romo9840/MFHL_Semesterprojekt_Security/Doku/Schaltplan_Widerstand_neu.png

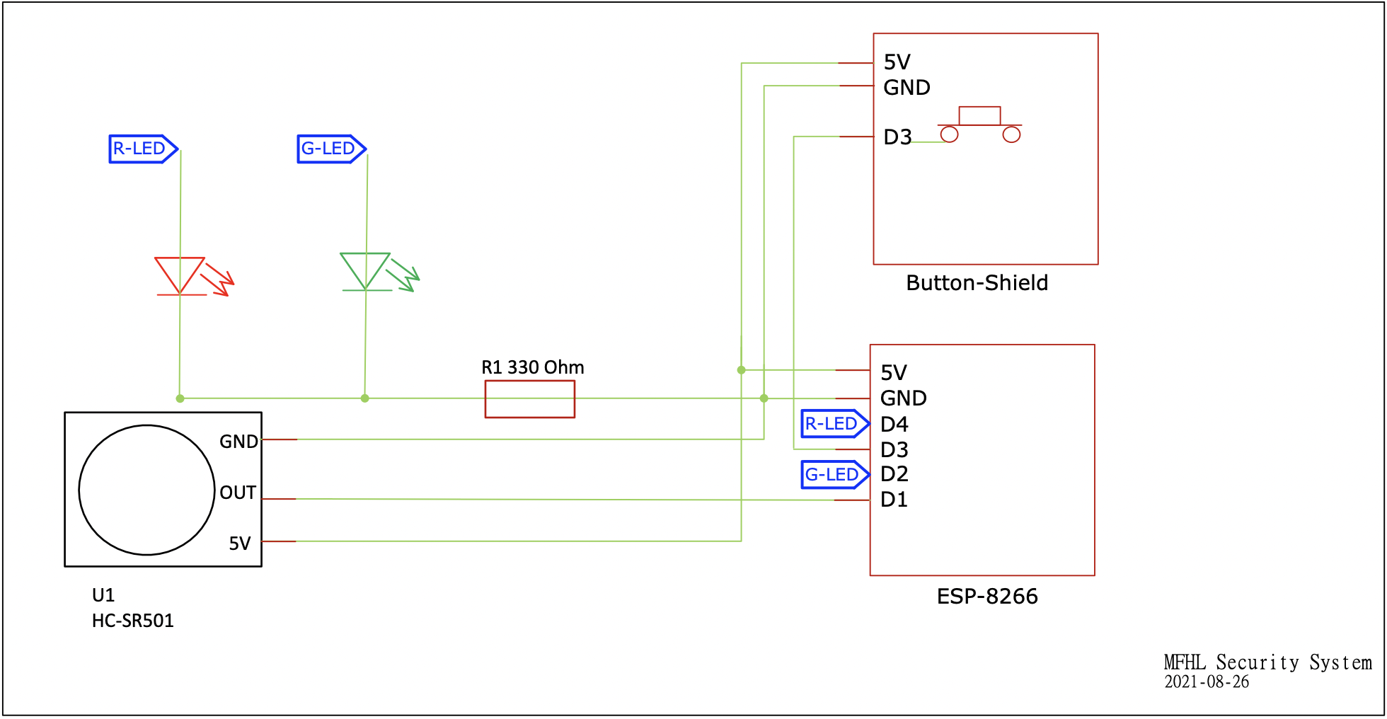
Doku/Schaltplan_Widerstand_neu.png
