romo9840/MFHL_Semesterprojekt_Security/Doku/Zustandsdiagramm_neu.png

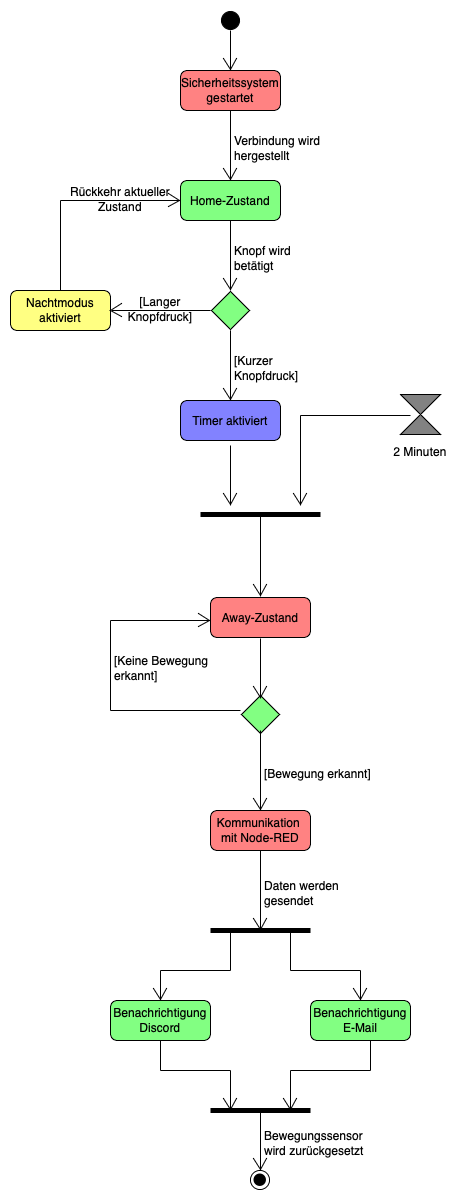
Doku/Zustandsdiagramm_neu.png
