romo9840/MFHL_Semesterprojekt_Security/Pictures/11.09_bare_front.jpg

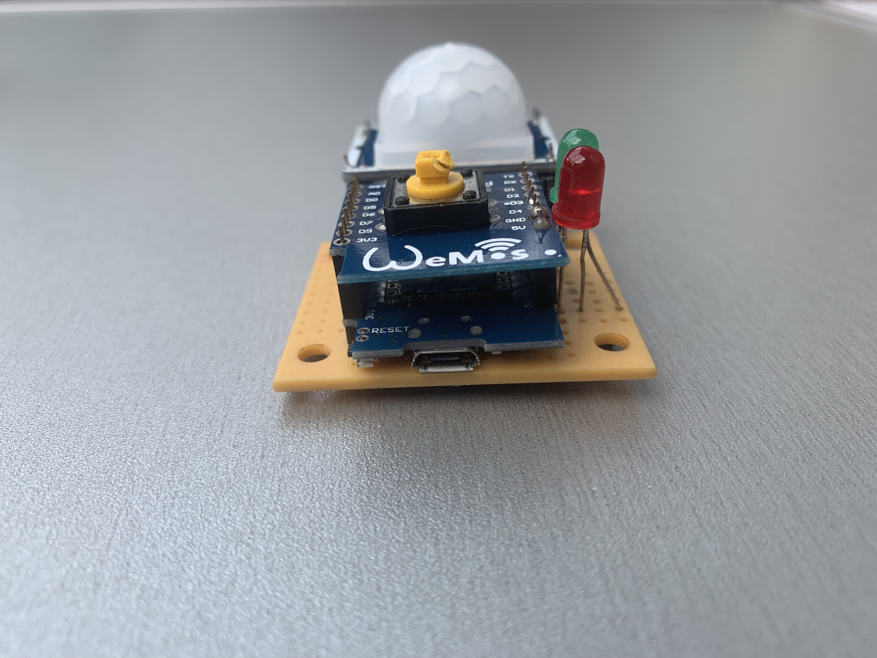
Pictures/11.09_bare_front.jpg
