romo9840/MFHL_Semesterprojekt_Security/Pictures/11.09_bare_other_side3.jpg

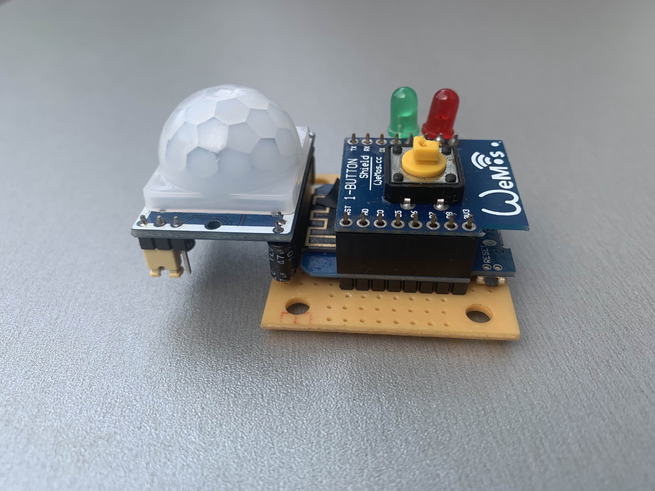
Pictures/11.09_bare_other_side3.jpg
