romo9840/MFHL_Semesterprojekt_Security/Pictures/11.09_bare_top_button.jpg

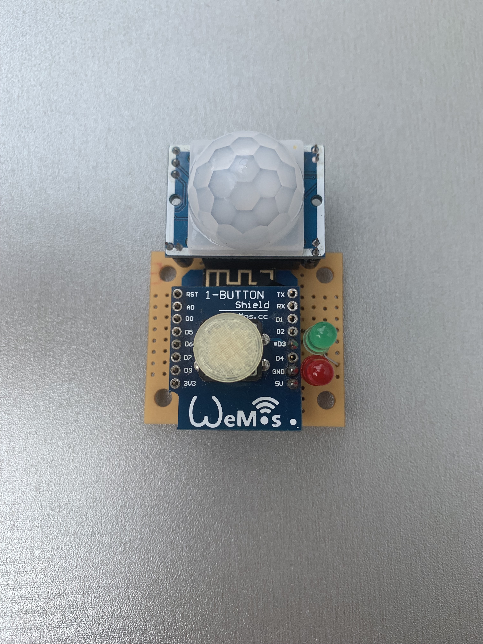
Pictures/11.09_bare_top_button.jpg
