romo9840/MFHL_Semesterprojekt_Security/Pictures/11.09_case_front.jpg

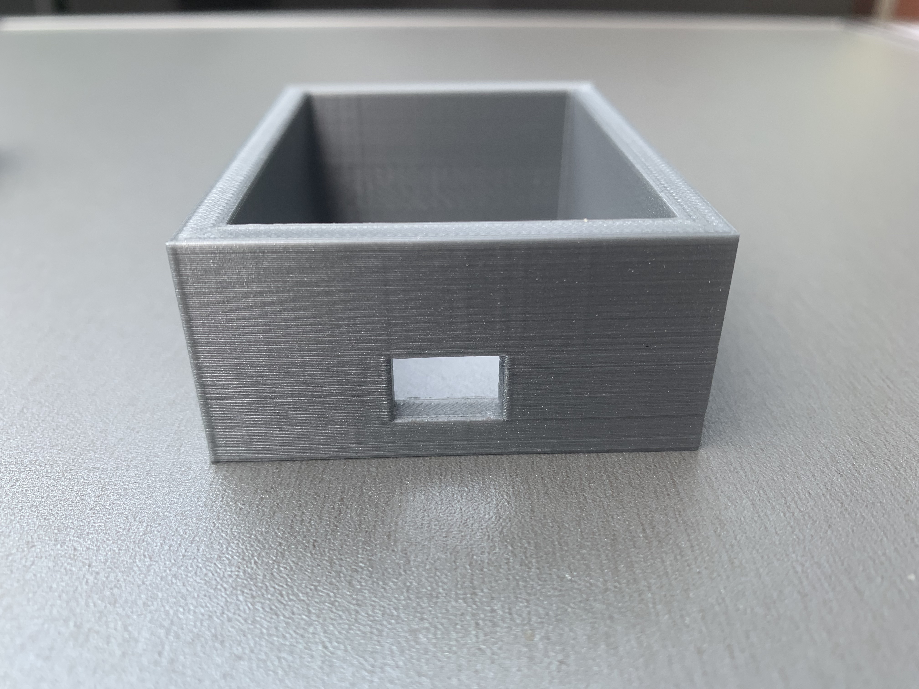
Pictures/11.09_case_front.jpg
