romo9840/MFHL_Semesterprojekt_Security/Pictures/11.09_closer_full_top.jpg

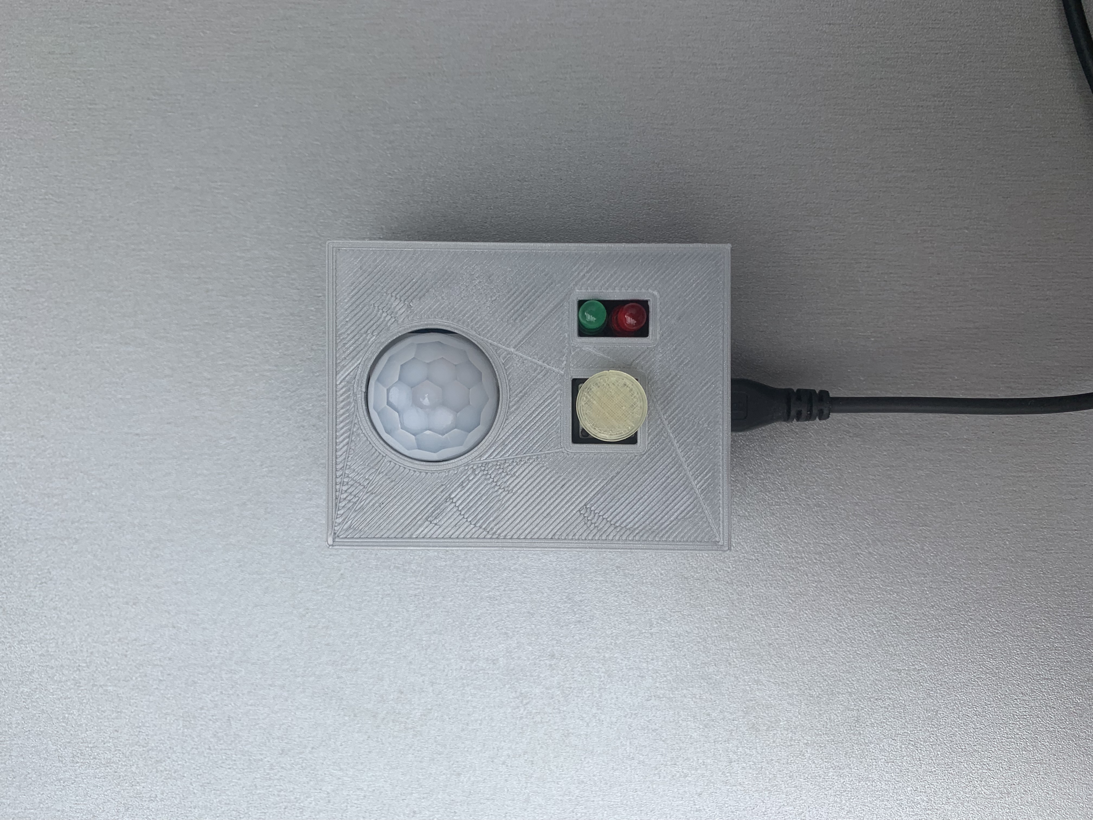
Pictures/11.09_closer_full_top.jpg
