romo9840/MFHL_Semesterprojekt_Security/Pictures/11.09_deckel_side.jpg

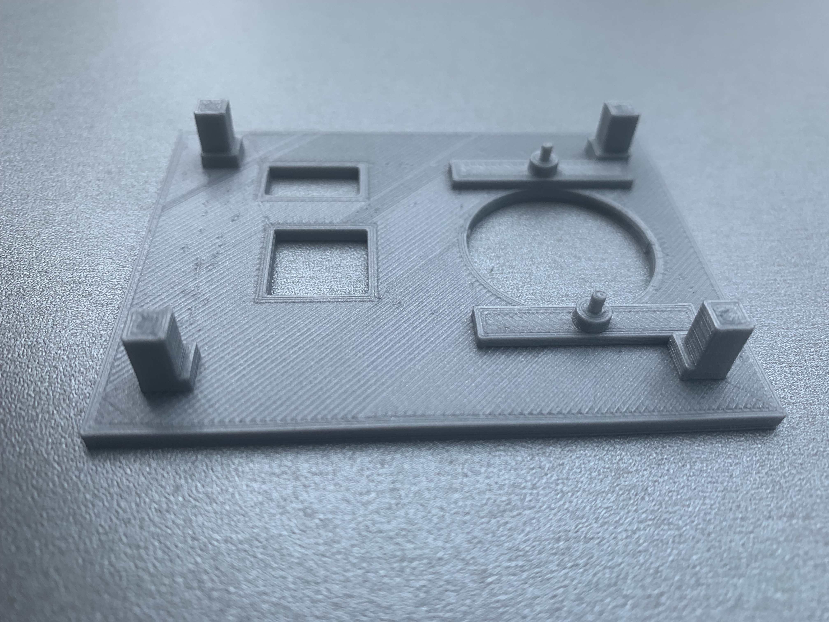
Pictures/11.09_deckel_side.jpg
