romo9840/MFHL_Semesterprojekt_Security/Pictures/11.09_open_top.jpg

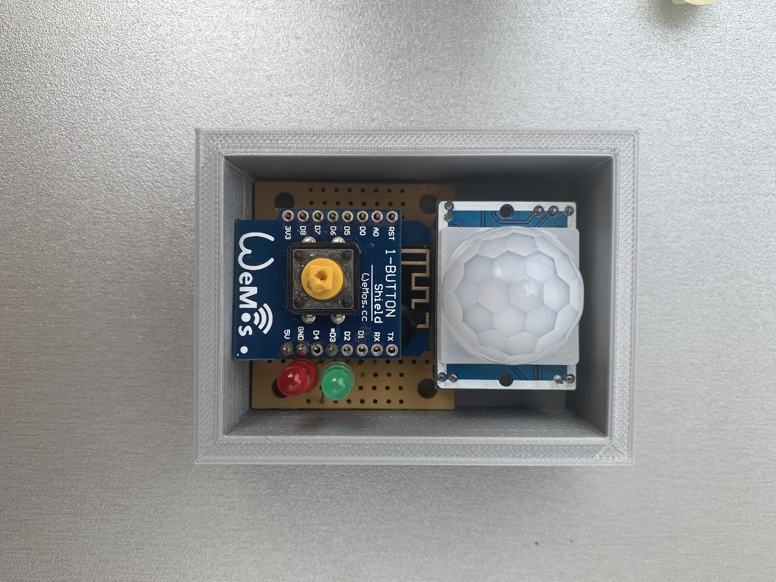
Pictures/11.09_open_top.jpg
