romo9840/MFHL_Semesterprojekt_Security/Pictures/11.09_sensor.jpg

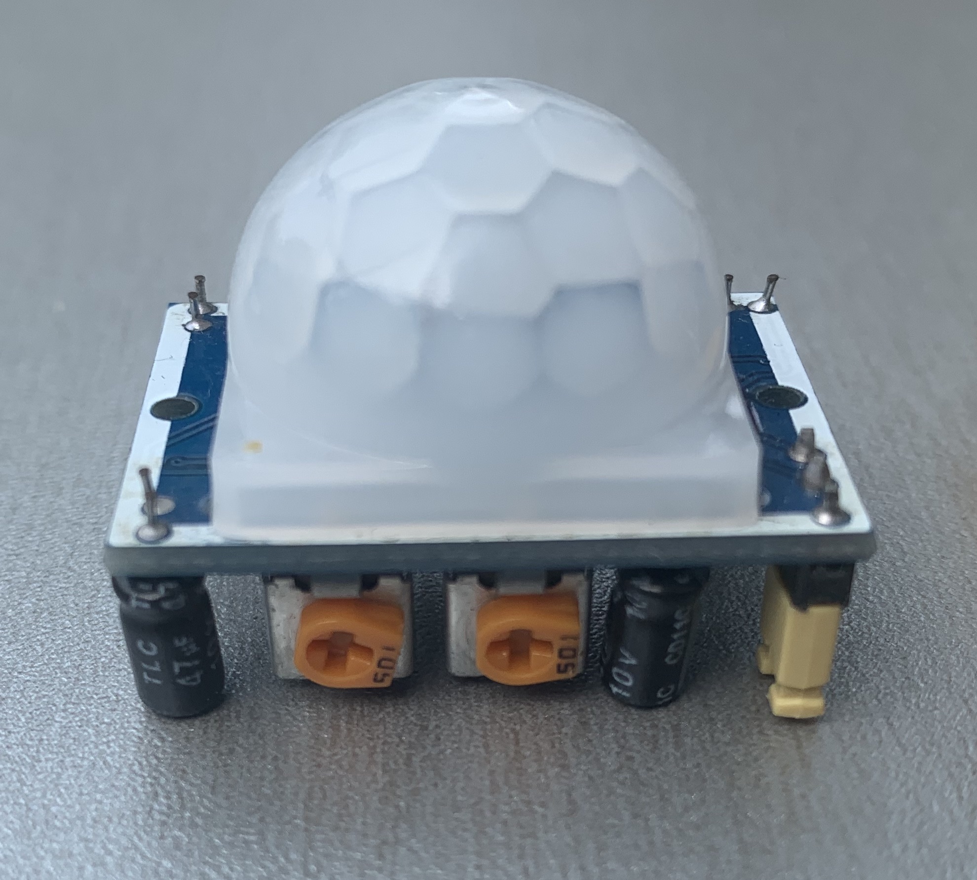
Pictures/11.09_sensor.jpg
