romo9840/MFHL_Semesterprojekt_Security/Pictures/19.08_Full_Top.jpg

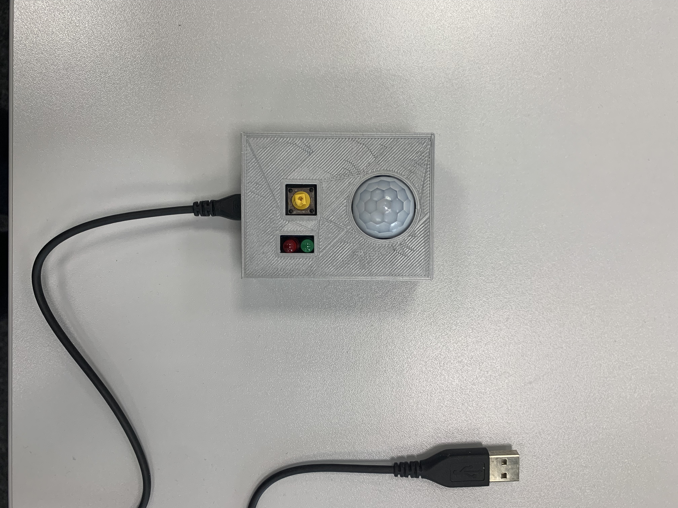
Pictures/19.08_Full_Top.jpg
