romo9840/MFHL_Semesterprojekt_Security/Pictures/19.08_Inside_Top.jpg

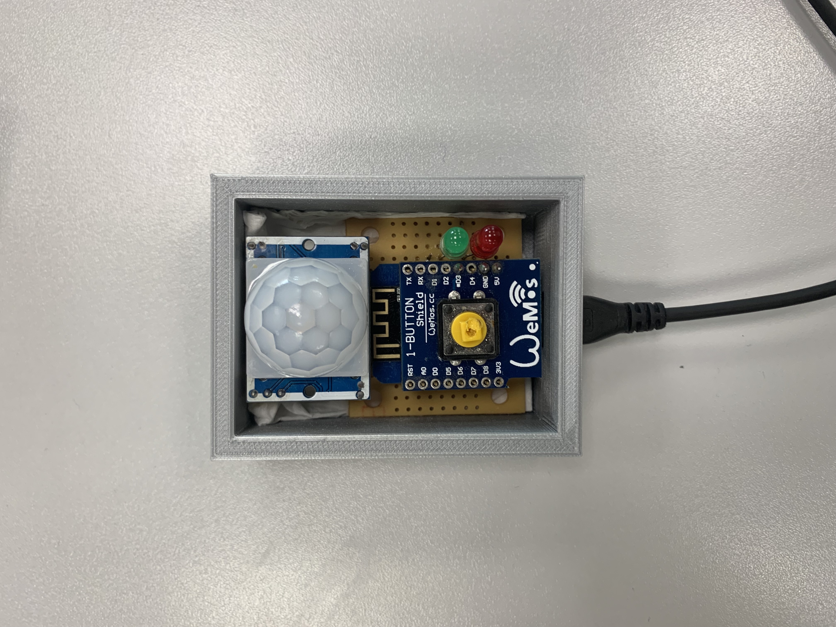
Pictures/19.08_Inside_Top.jpg
