romo9840/MFHL_Semesterprojekt_Security/Pictures/22.07_Back_Top.jpg

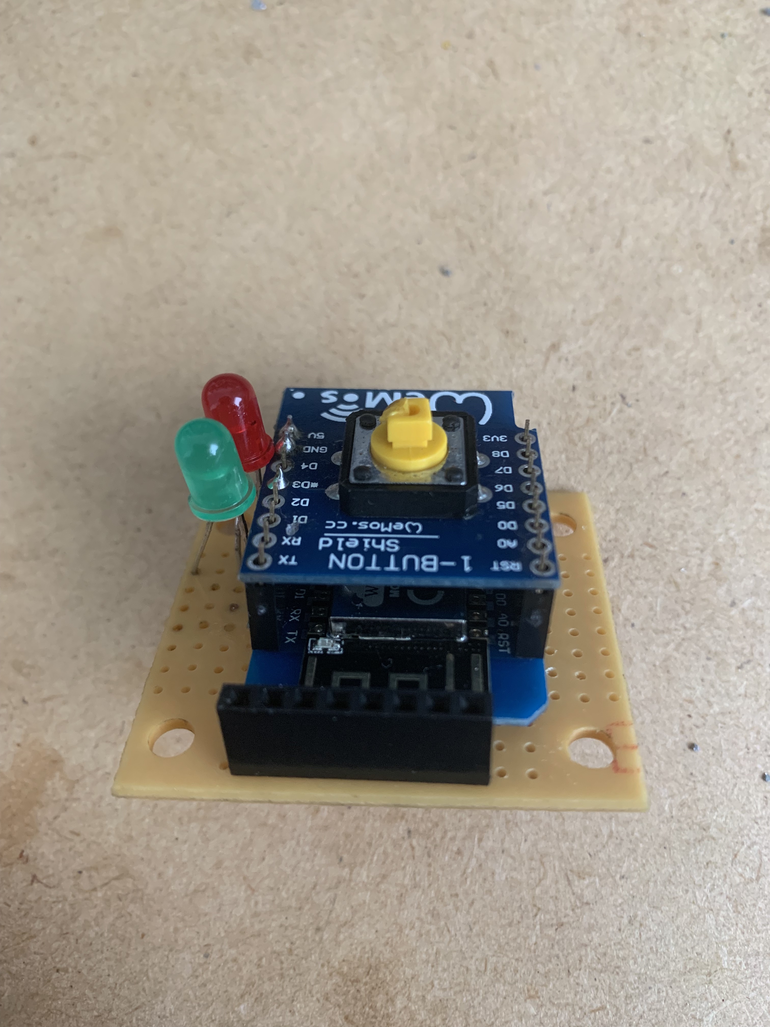
Pictures/22.07_Back_Top.jpg
