romo9840/MFHL_Semesterprojekt_Security/Pictures/22.07_Lötstellen.jpg

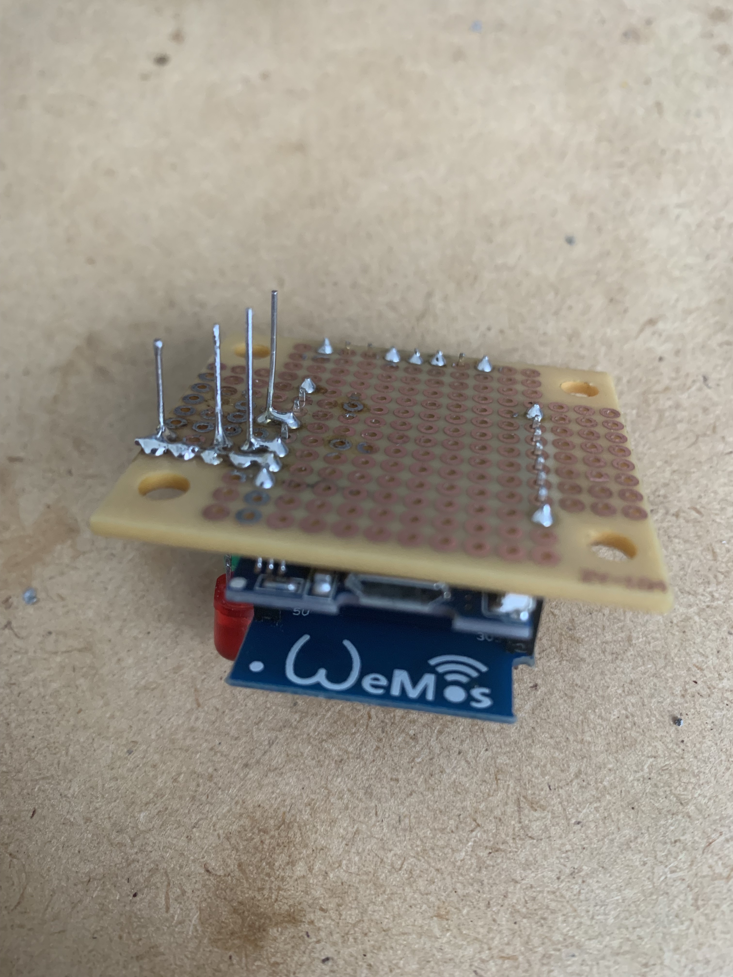
Pictures/22.07_Lötstellen.jpg
