romo9840/MFHL_Semesterprojekt_Security/Pictures/27.07_Top.jpg

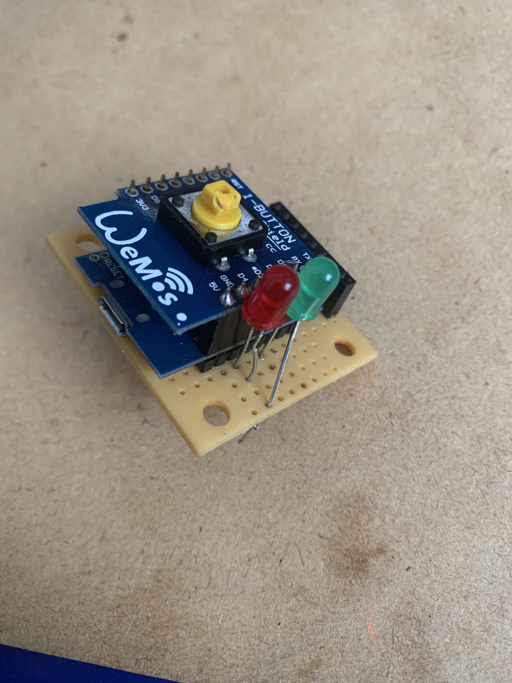
Pictures/27.07_Top.jpg
