romo9840/MFHL_Semesterprojekt_Security/Pictures/Abmessungen Körper.png

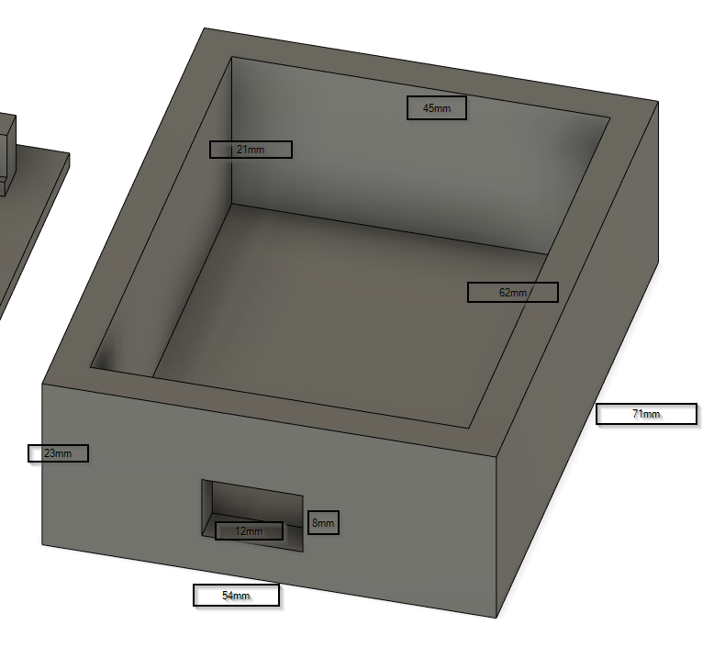
Pictures/Abmessungen Körper.png
