romo9840/MFHL_Semesterprojekt_Security/Pictures/Projekt_Schaltung_05.jpg

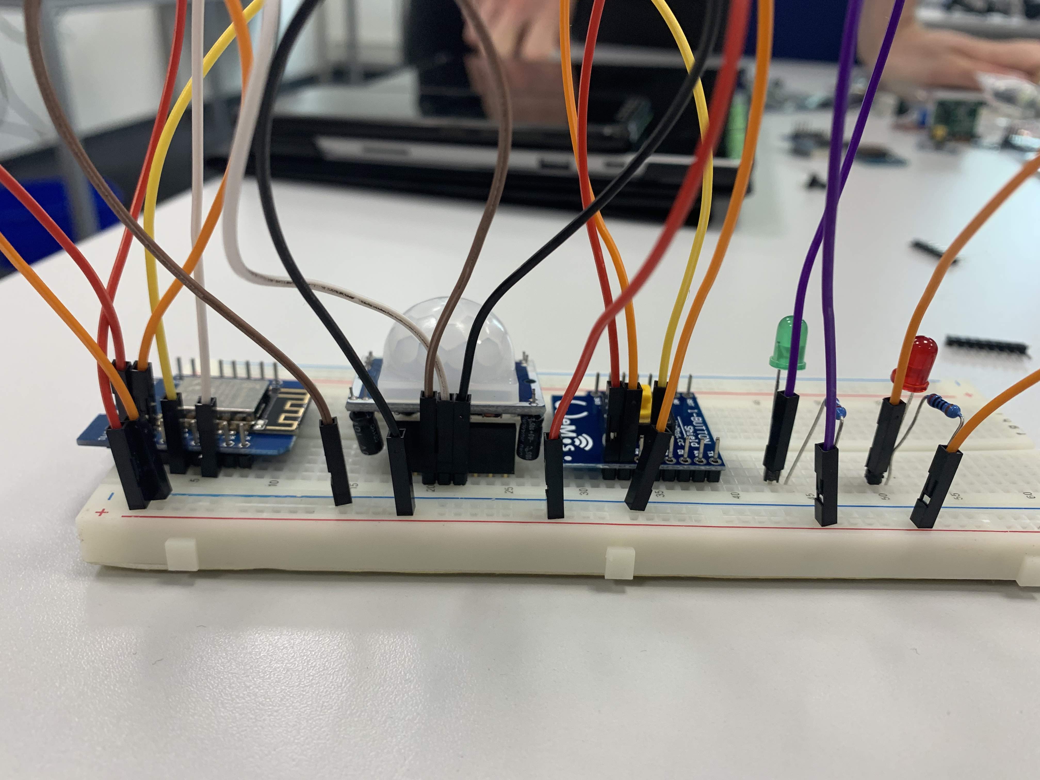
Pictures/Projekt_Schaltung_05.jpg
